CircuitSetup/Expandable-6-Channel-ESP32-Energy-Meter/Images/6-channel_v1.3_back.jpg

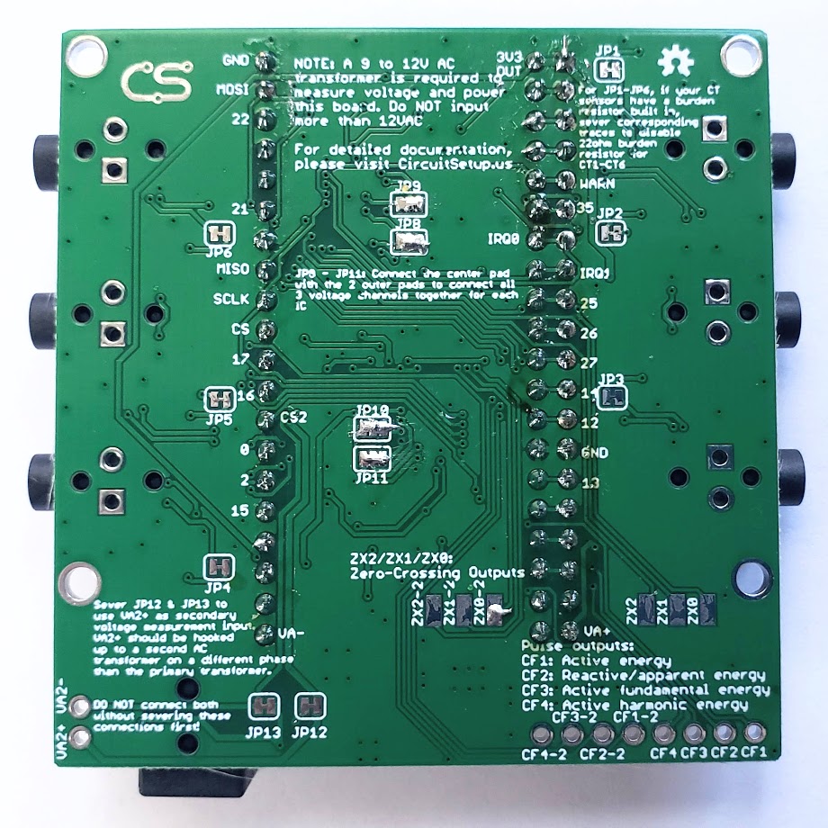
Images/6-channel_v1.3_back.jpg
