CircuitSetup/Expandable-6-Channel-ESP32-Energy-Meter/Images/20191108_202555.jpg

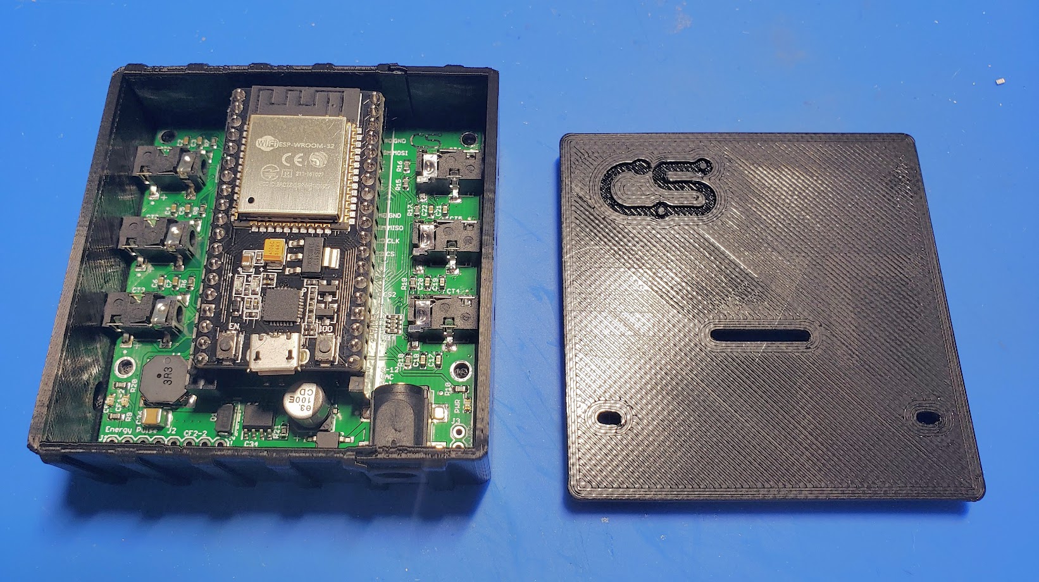
Images/20191108_202555.jpg
