CircuitSetup/Expandable-6-Channel-ESP32-Energy-Meter/Images/20191108_203225.jpg

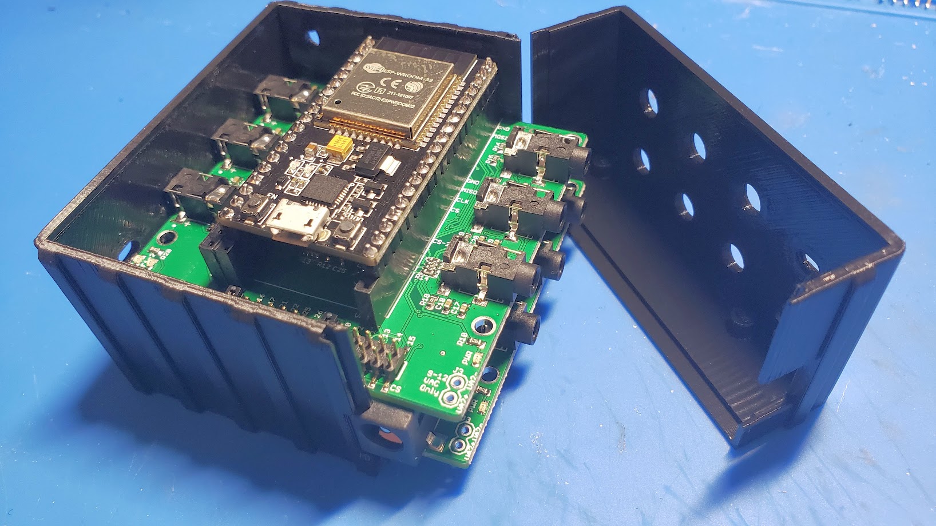
Images/20191108_203225.jpg
