CircuitSetup/Expandable-6-Channel-ESP32-Energy-Meter/Images/atm90e32-cs-6chan-full-large.jpg

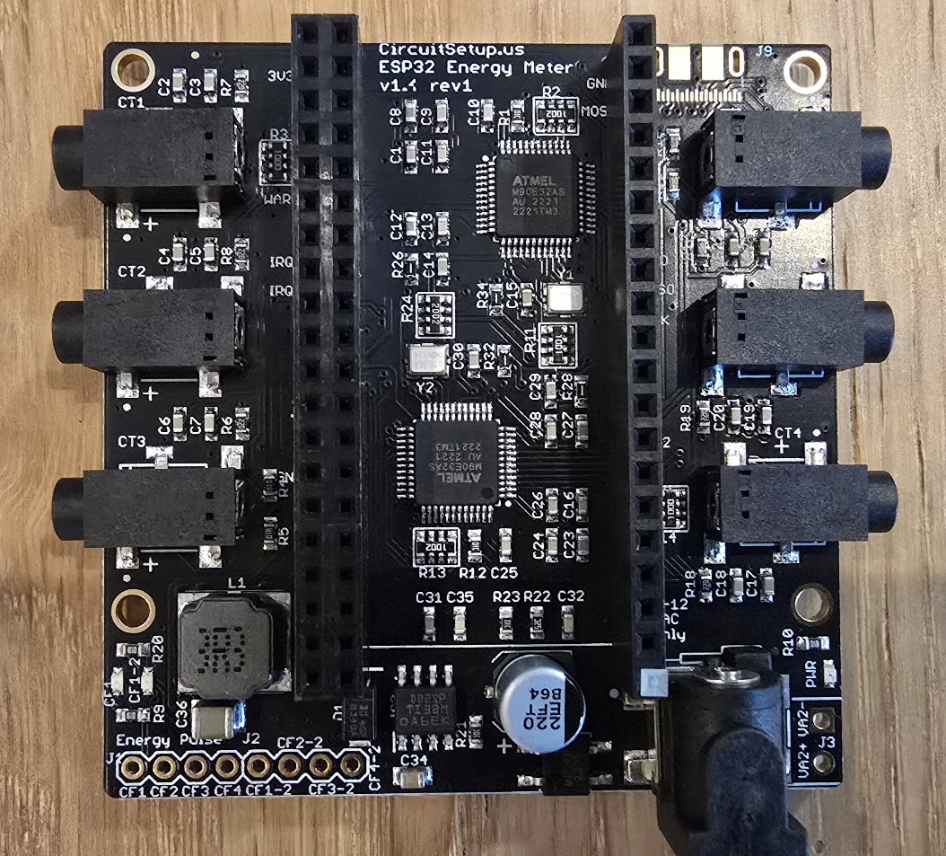
Images/atm90e32-cs-6chan-full-large.jpg
