CircuitSetup/Expandable-6-Channel-ESP32-Energy-Meter/Images/download_binary.png

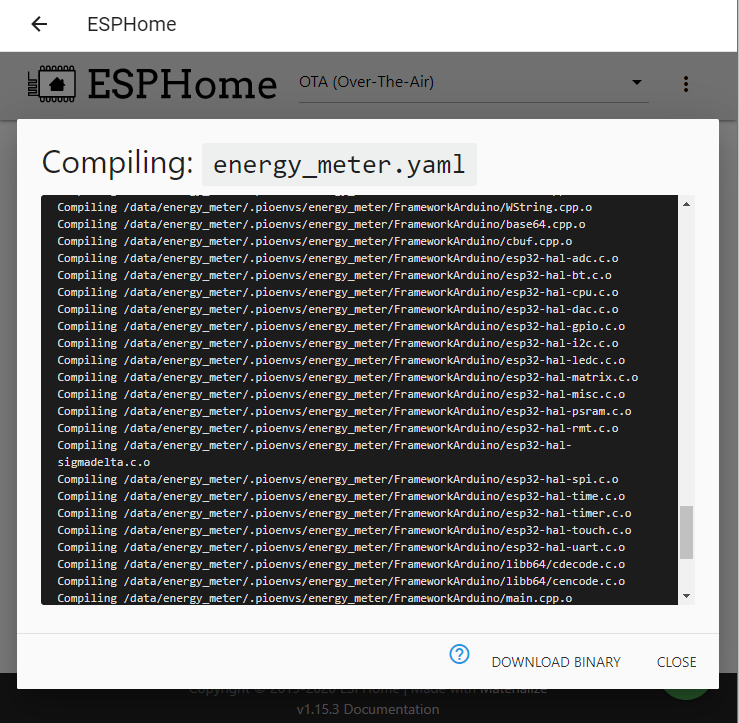
Images/download_binary.png
