CircuitSetup/Expandable-6-Channel-ESP32-Energy-Meter/Images/esphome_flasher.PNG

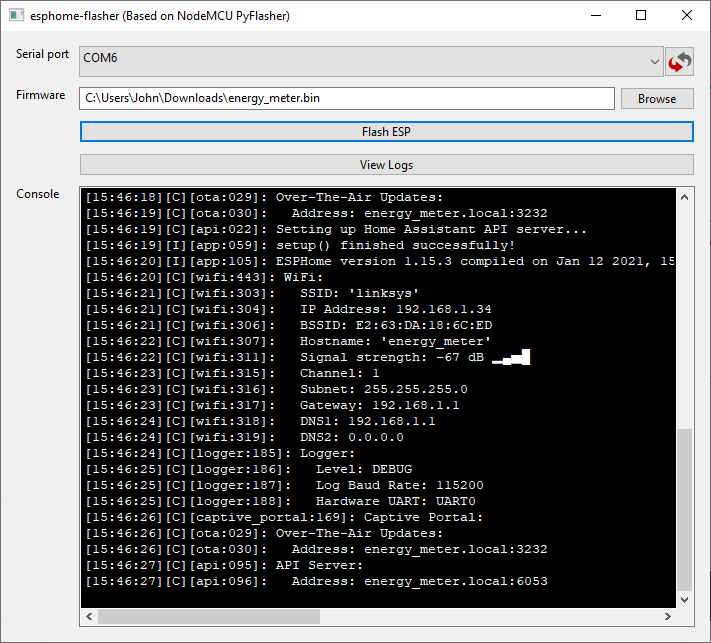
Images/esphome_flasher.PNG
