CircuitSetup/Expandable-6-Channel-ESP32-Energy-Meter/Images/esphome_main.png

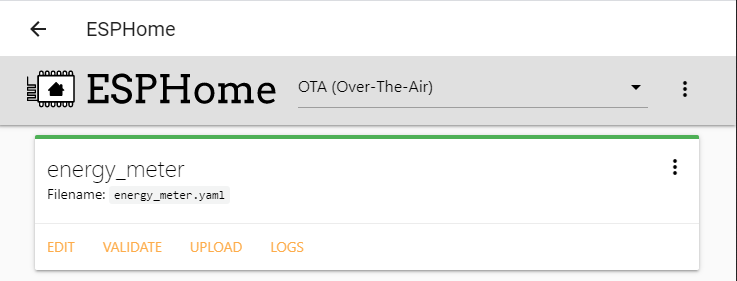
Images/esphome_main.png
