CircuitSetup/Expandable-6-Channel-ESP32-Energy-Meter/Images/home_assistant_energy2.PNG

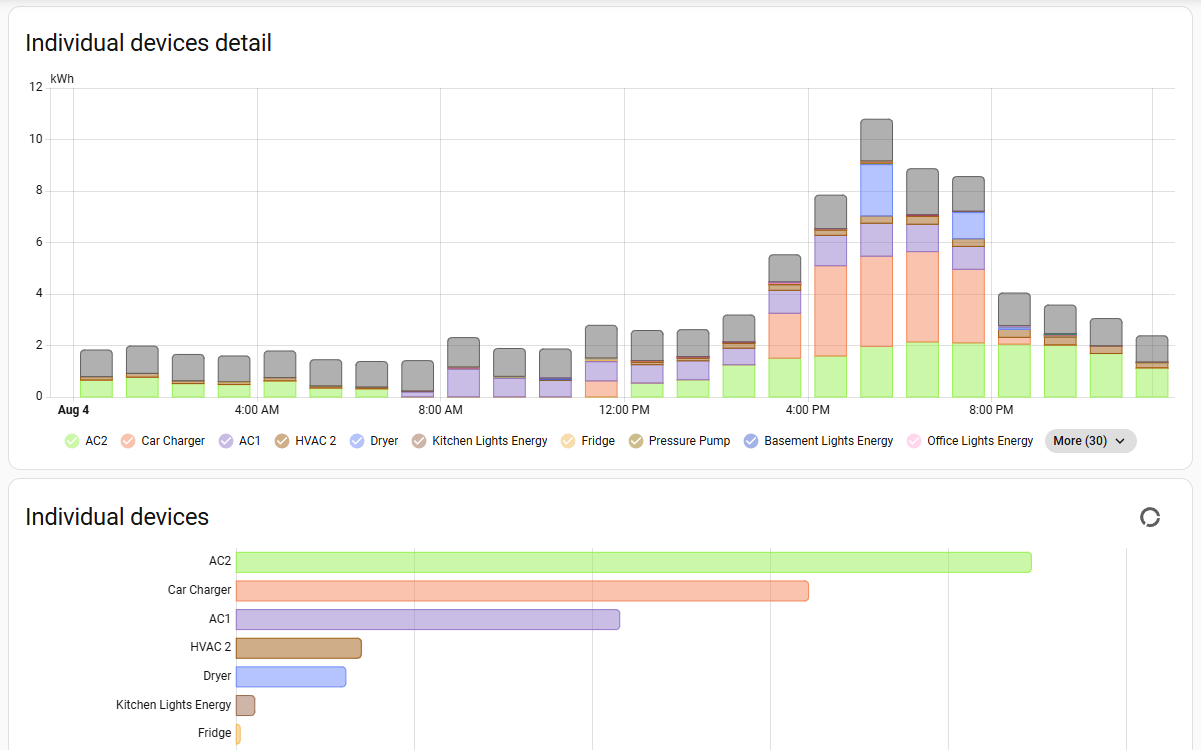
Images/home_assistant_energy2.PNG
