CircuitSetup/Expandable-6-Channel-ESP32-Energy-Meter/Software/EmonESP/docs/emoncms.png

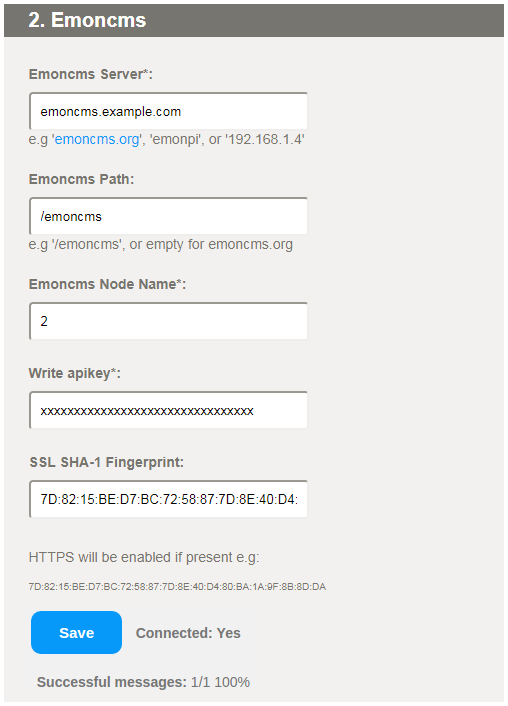
Software/EmonESP/docs/emoncms.png
