CircuitSetup/Expandable-6-Channel-ESP32-Energy-Meter/Software/EmonESP/docs/emonesp.png

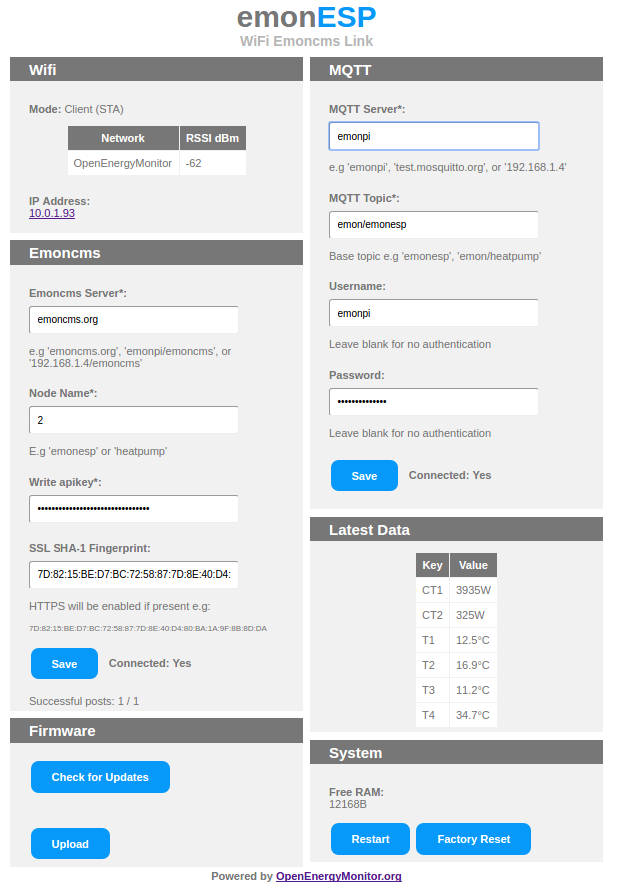
Software/EmonESP/docs/emonesp.png
