CircuitSetup/Expandable-6-Channel-ESP32-Energy-Meter/Software/EmonESP/docs/input.png

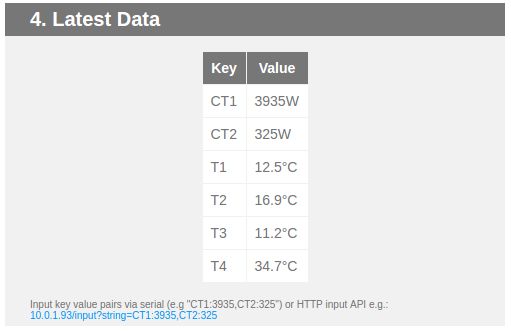
Software/EmonESP/docs/input.png
