CircuitSetup/Expandable-6-Channel-ESP32-Energy-Meter/Software/EmonESP/docs/wifi.png

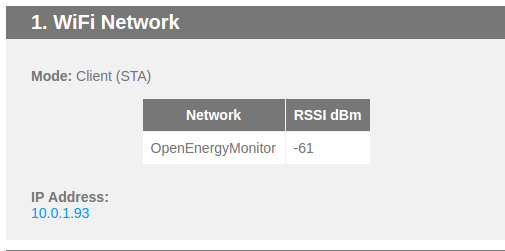
Software/EmonESP/docs/wifi.png
