CircuitSetup/Expandable-6-Channel-ESP32-Energy-Meter/Hardware/6channel_energy_meter_2piece_case_cover.stl

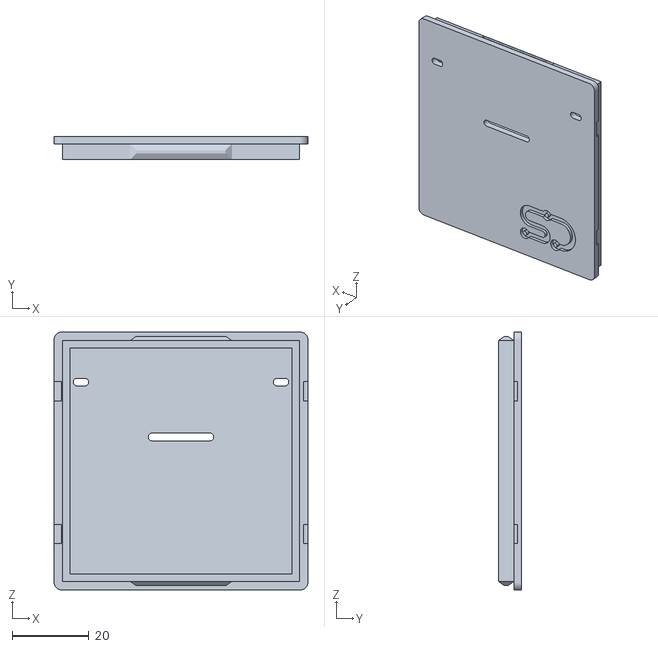
[picture p42: CAD file, 2019-11-10]
Hardware/6channel_energy_meter_2piece_case_cover.stl
66.0 x 6.00 x 67.0
