CircuitSetup/Expandable-6-Channel-ESP32-Energy-Meter/Hardware/Ethernet Adapter Cases/6channel_energy_meter_2piece_case_5-addon_ethernet_ws_large_half.stl

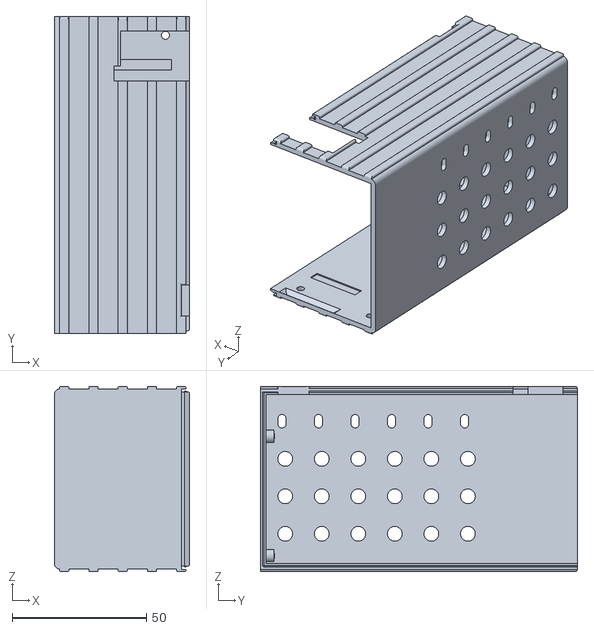
[picture p44: CAD file, 2026-02-12]
Hardware/Ethernet Adapter Cases/6channel_energy_meter_2piece_case_5-addon_ethernet_ws_large_half.stl
50.3 x 118.0 x 69.0
