CircuitSetup/Expandable-6-Channel-ESP32-Energy-Meter/Hardware/Ethernet Adapter Cases/6channel_energy_meter_2piece_case_1-addon_ethernet_ws_small_half.stl

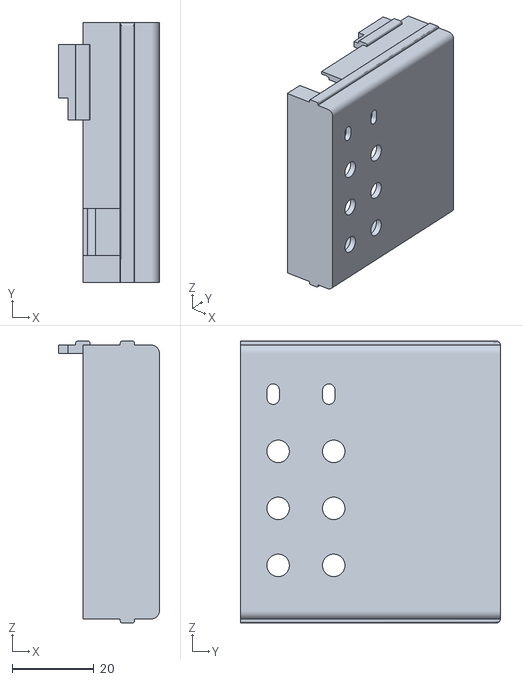
[picture p47: CAD file, 2026-02-12]
Hardware/Ethernet Adapter Cases/6channel_energy_meter_2piece_case_1-addon_ethernet_ws_small_half.stl
24.7 x 63.6 x 69.0
