CircuitSetup/Expandable-6-Channel-ESP32-Energy-Meter/Hardware/6channel_energy_meter_2piece_case_1-addon_small_half.stl

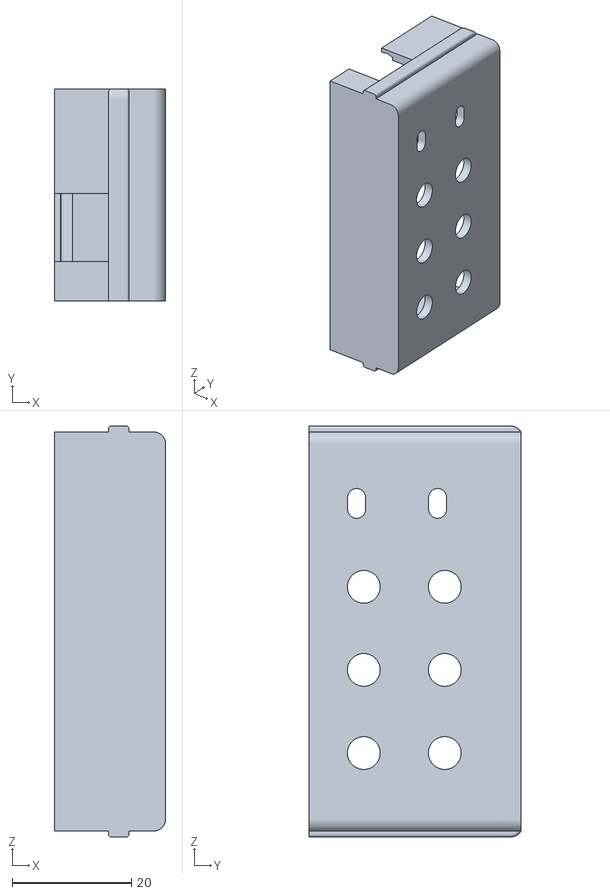
[picture p50: CAD file, 2019-11-10]
Hardware/6channel_energy_meter_2piece_case_1-addon_small_half.stl
18.6 x 35.6 x 69.0
