CircuitSetup/Expandable-6-Channel-ESP32-Energy-Meter/Hardware/Ethernet Adapter Cases/6channel_energy_meter_2piece_case_5-addon_ethernet_small_half.stl

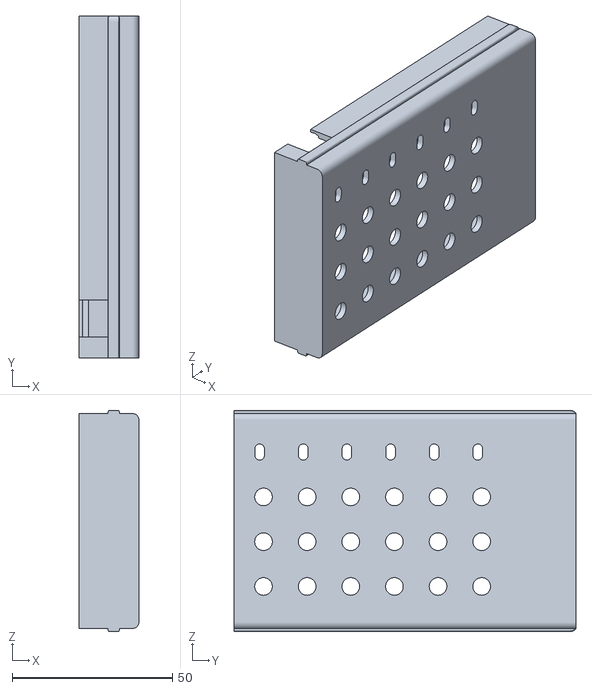
[picture p53: CAD file, 2024-08-21]
Hardware/Ethernet Adapter Cases/6channel_energy_meter_2piece_case_5-addon_ethernet_small_half.stl
18.7 x 106.6 x 69.0
