CircuitSetup/Expandable-6-Channel-ESP32-Energy-Meter/Hardware/6channel_case.stl

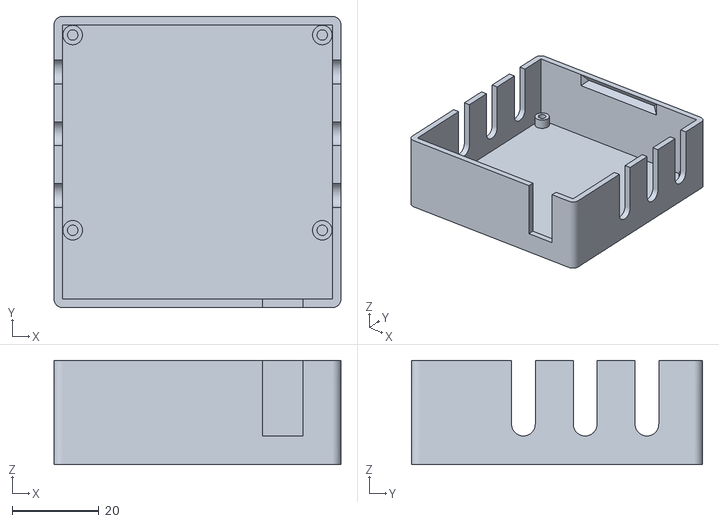
[picture p54: CAD file, 2019-10-14]
Hardware/6channel_case.stl
66.0 x 67.0 x 24.0
