CircuitSetup/Expandable-6-Channel-ESP32-Energy-Meter/Hardware/6channel_meter_case.stl

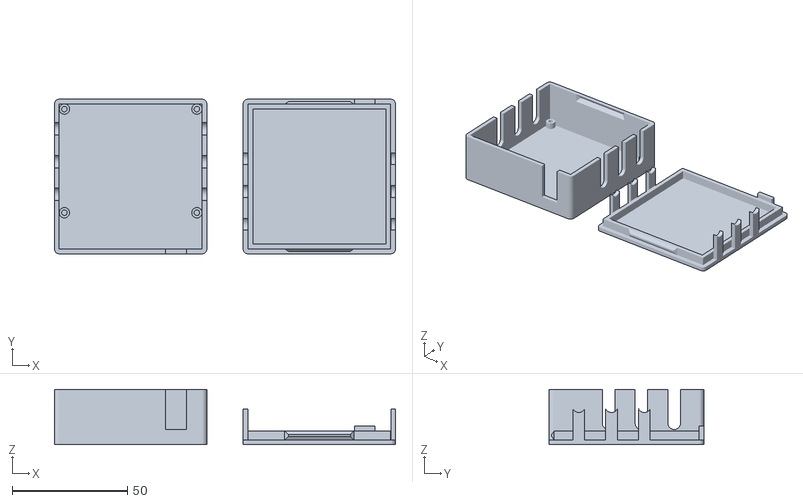
[picture p56: CAD file, 2019-10-14]
Hardware/6channel_meter_case.stl
147.7 x 67.0 x 24.0
