CircuitSetup/Expandable-6-Channel-ESP32-Energy-Meter/Hardware/Ethernet Adapter Cases/6channel_energy_meter_2piece_case_3-addon_ethernet_large_half.stl

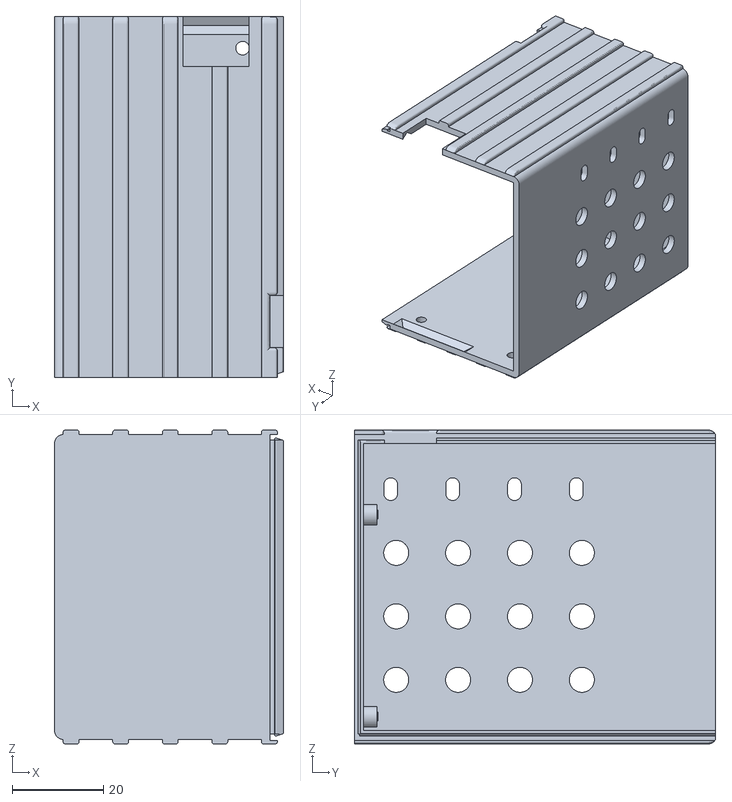
[picture p57: CAD file, 2024-08-21]
Hardware/Ethernet Adapter Cases/6channel_energy_meter_2piece_case_3-addon_ethernet_large_half.stl
50.3 x 79.4 x 69.0
