CircuitSetup/Expandable-6-Channel-ESP32-Energy-Meter/Hardware/6channel_case_lid.stl

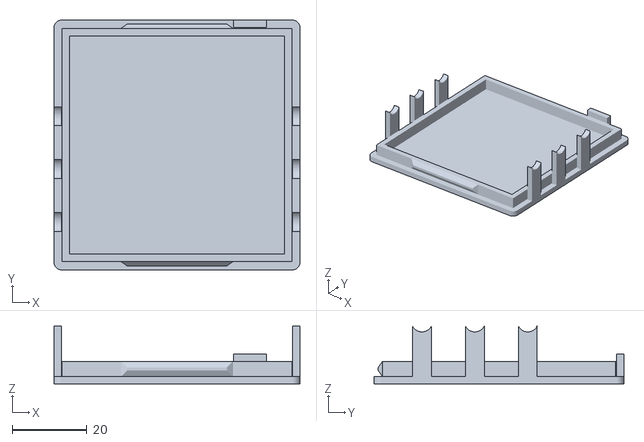
[picture p58: CAD file, 2019-10-14]
Hardware/6channel_case_lid.stl
66.0 x 67.0 x 15.5
