CircuitSetup/Expandable-6-Channel-ESP32-Energy-Meter/Images/esphome_gain_calibration.PNG

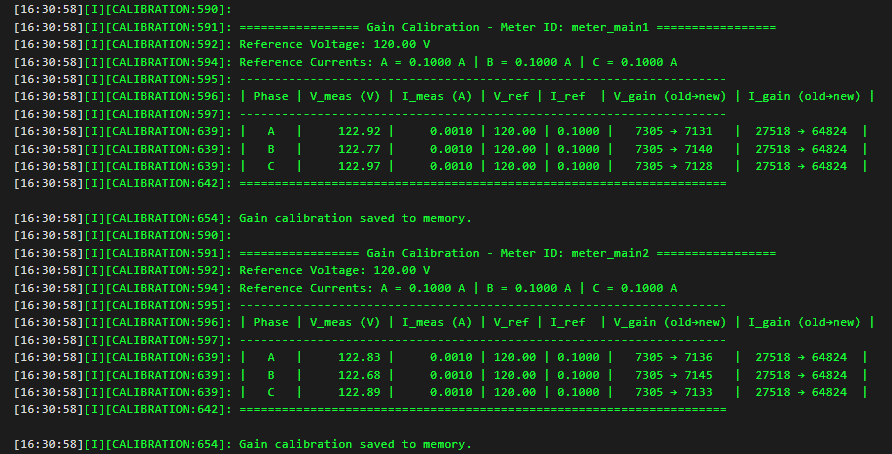
Images/esphome_gain_calibration.PNG
