CircuitSetup/Expandable-6-Channel-ESP32-Energy-Meter/Software/ESPHome/meter_sensors/6chan_addon3.yaml

# CircuitSetup 6 Channel Energy Meter 3rd Add-on board config
# Assumes jumpers are both in the 3rd position

sensor:
#IC1 AddOn 3
############
  - platform: atm90e32
    release_device: true
    #if ESP32 has an LED for GPIO2, remove jumper or ESP32 from meter stack before programming via serial
    cs_pin: 2
    id: ${addon3_id1}
    phase_a:
      voltage:
        name: "${addon3_name1} Voltage A Calibration"
        id: addon3_1_voltage_a_calibration
        accuracy_decimals: 2
        entity_category: diagnostic
        disabled_by_default: true
      current:
        name: ${ct19_name} Amps
        id: ct19Amps
      power:
        name: ${ct19_name} Watts
        id: ct19Watts
      gain_voltage: ${voltage_cal1}
      gain_ct: ${current_cal_ct19}
    phase_b:
      voltage:
        name: "${addon3_name1} Voltage B Calibration"
        id: addon3_1_voltage_b_calibration
        accuracy_decimals: 2
        entity_category: diagnostic
        disabled_by_default: true
      current:
        name: ${ct20_name} Amps
        id: ct20Amps
      power:
        name: ${ct20_name} Watts
        id: ct20Watts
      gain_voltage: ${voltage_cal1}
      gain_ct: ${current_cal_ct20}
    phase_c:
      voltage:
        name: "${addon3_name1} Voltage C Calibration"
        id: addon3_1_voltage_c_calibration
        accuracy_decimals: 2
        entity_category: diagnostic
        disabled_by_default: true
      current:
        name: ${ct21_name} Amps
        id: ct21Amps
      power:
        name: ${ct21_name} Watts
        id: ct21Watts
      gain_voltage: ${voltage_cal1}
      gain_ct: ${current_cal_ct21}
    line_frequency: ${electric_freq}
    gain_pga: 1X
    update_interval: ${update_time}
    enable_offset_calibration: ${offset_calibration}
    enable_gain_calibration: ${gain_calibration}
#IC2 AddOn 3
############
  - platform: atm90e32
    release_device: true
    cs_pin: 21
    id: ${addon3_id2}
    phase_a:
      voltage:
        name: "${addon3_name2} Voltage A Calibration"
        id: addon3_2_voltage_a_calibration
        accuracy_decimals: 2
        entity_category: diagnostic
        disabled_by_default: true
      current:
        name: ${ct22_name} Amps
        id: ct22Amps
      power:
        name: ${ct22_name} Watts
        id: ct22Watts
      gain_voltage: ${voltage_cal2}
      gain_ct: ${current_cal_ct22}
    phase_b:
      voltage:
        name: "${addon3_name2} Voltage B Calibration"
        id: addon3_2_voltage_b_calibration
        accuracy_decimals: 2
        entity_category: diagnostic
        disabled_by_default: true
      current:
        name: ${ct23_name} Amps
        id: ct23Amps
      power:
        name: ${ct23_name} Watts
        id: ct23Watts
      gain_voltage: ${voltage_cal2}
      gain_ct: ${current_cal_ct23}
    phase_c:
      voltage:
        name: "${addon3_name2} Voltage C Calibration"
        id: addon3_2_voltage_c_calibration
        accuracy_decimals: 2
        entity_category: diagnostic
        disabled_by_default: true
      current:
        name: ${ct24_name} Amps
        id: ct24Amps
      power:
        name: ${ct24_name} Watts
        id: ct24Watts
      gain_voltage: ${voltage_cal2}
      gain_ct: ${current_cal_ct24}
    line_frequency: ${electric_freq}
    gain_pga: 1X
    update_interval: ${update_time}
    enable_offset_calibration: ${offset_calibration}
    enable_gain_calibration: ${gain_calibration}

#Total Amps AddOn3
  - platform: template
    name: ${friendly_name} Total Amps Add-on3
    id: totalAmpsAddOn3
    lambda: return id(ct19Amps).state + id(ct20Amps).state + id(ct21Amps).state + id(ct22Amps).state + id(ct23Amps).state + id(ct24Amps).state ;
    accuracy_decimals: 2
    unit_of_measurement: A
    device_class: current
    update_interval: ${update_time}

#Total Watts AddOn3
  - platform: template
    name: ${friendly_name} Total Watts Add-on3
    id: totalWattsAddOn3
    lambda: return id(ct19Watts).state + id(ct20Watts).state + id(ct21Watts).state + id(ct22Watts).state + id(ct23Watts).state + id(ct24Watts).state ;
    accuracy_decimals: 2
    unit_of_measurement: W
    device_class: power
    update_interval: ${update_time}
