CircuitSetup/Expandable-6-Channel-ESP32-Energy-Meter/Software/ESPHome/calibration/6chan_addon1_calibration.yaml

# Details: https://esphome.io/components/sensor/atm90e32.html#calibration
# Semi-automatic Calibration Buttons
####################################
button:
  - platform: atm90e32
    id: ${addon1_id1}
    run_offset_calibration:
      name: "1. Run ${addon1_name1} Offset Cal"
      disabled_by_default: true
    clear_offset_calibration:
      name: "z1. Clear ${addon1_name1} Offset Cal"
      disabled_by_default: true
    run_power_offset_calibration:
      name: "2. Run ${addon1_name1} Power Offset Cal"
      disabled_by_default: true
    clear_power_offset_calibration:
      name: "z2. Clear ${addon1_name1} Power Offset Cal"
      disabled_by_default: true
    run_gain_calibration:
      name: "3. Run ${addon1_name1} Gain Cal"
      disabled_by_default: true
    clear_gain_calibration:
      name: "z3. Clear ${addon1_name1} Gain Cal"
      disabled_by_default: true

  - platform: atm90e32
    id: ${addon1_id2}
    run_offset_calibration:
      name: "1. Run ${addon1_name2} Offset Cal"
      disabled_by_default: true
    clear_offset_calibration:
      name: "z1. Clear ${addon1_name2} Offset Cal"
      disabled_by_default: true
    run_power_offset_calibration:
      name: "2. Run ${addon1_name2} Power Offset Cal"
      disabled_by_default: true
    clear_power_offset_calibration:
      name: "z2. Clear ${addon1_name2} Power Offset Cal"
      disabled_by_default: true
    run_gain_calibration:
      name: "3. Run ${addon1_name2} Gain Cal"
      disabled_by_default: true
    clear_gain_calibration:
      name: "z3. Clear ${addon1_name2} Gain Cal"
      disabled_by_default: true

# V & I Calibration Reference Fields
####################################
# Use these to input a known value being measured by a CT or voltage transformer
number:
  - platform: atm90e32
    id: ${addon1_id1}
    reference_voltage:
      # will copy to phase_b/c for calibration reference
      phase_a:
        name: "${addon1_name1} Ref V 1"
        min_value: 0.0
        max_value: 260.0
        step: 0.1
        disabled_by_default: true
    reference_current:
      phase_a:
        name: "${ct7_name} Ref Current"
        min_value: 0.0
        max_value: 200.0
        step: 0.1
        disabled_by_default: true
      phase_b:
        name: "${ct8_name} Ref Current"
        min_value: 0.0
        max_value: 200.0
        step: 0.1
        disabled_by_default: true
      phase_c:
        name: "${ct9_name} Ref Current"
        min_value: 0.0
        max_value: 200.0
        step: 0.1
        disabled_by_default: true

  - platform: atm90e32
    id: ${addon1_id2}
    reference_voltage:
      # needed to calibrate voltage registers even if not output
      phase_a:
        name: "${addon1_name2} Ref V 2" 
        min_value: 0.0
        max_value: 260.0
        step: 0.1
        disabled_by_default: true
    reference_current:
      phase_a:
        name: "${ct10_name} Ref Current"
        min_value: 0.0
        max_value: 200.0
        step: 0.1
        disabled_by_default: true
      phase_b:
        name: "${ct11_name} Ref Current"
        min_value: 0.0
        max_value: 200.0
        step: 0.1
        disabled_by_default: true
      phase_c:
        name: "${ct12_name} Ref Current"
        min_value: 0.0
        max_value: 200.0
        step: 0.1
        disabled_by_default: true
