CircuitSetup/Expandable-6-Channel-ESP32-Energy-Meter/Software/ESPHome/calibration/6chan_addon2_calibration.yaml

# Details: https://esphome.io/components/sensor/atm90e32.html#calibration
# Semi-automatic Calibration Buttons
####################################
button:
  - platform: atm90e32
    id: ${addon2_id1}
    run_offset_calibration:
      name: "1. Run ${addon2_name1} Offset Cal"
      disabled_by_default: true
    clear_offset_calibration:
      name: "z1. Clear ${addon2_name1} Offset Cal"
      disabled_by_default: true
    run_power_offset_calibration:
      name: "2. Run ${addon2_name1} Power Offset Cal"
      disabled_by_default: true
    clear_power_offset_calibration:
      name: "z2. Clear ${addon2_name1} Power Offset Cal"
      disabled_by_default: true
    run_gain_calibration:
      name: "3. Run ${addon2_name1} Gain Cal"
      disabled_by_default: true
    clear_gain_calibration:
      name: "z3. Clear ${addon2_name1} Gain Cal"
      disabled_by_default: true

  - platform: atm90e32
    id: ${addon2_id2}
    run_offset_calibration:
      name: "1. Run ${addon2_name2} Offset Cal"
      disabled_by_default: true
    clear_offset_calibration:
      name: "z1. Clear ${addon2_name2} Offset Cal"
      disabled_by_default: true
    run_power_offset_calibration:
      name: "2. Run ${addon2_name2} Power Offset Cal"
      disabled_by_default: true
    clear_power_offset_calibration:
      name: "z2. Clear ${addon2_name2} Power Offset Cal"
      disabled_by_default: true
    run_gain_calibration:
      name: "3. Run ${addon2_name2} Gain Cal"
      disabled_by_default: true
    clear_gain_calibration:
      name: "z3. Clear ${addon2_name2} Gain Cal"
      disabled_by_default: true

# V & I Calibration Reference Fields
####################################
# Use these to input a known value being measured by a CT or voltage transformer
number:
  - platform: atm90e32
    id: ${addon2_id1}
    reference_voltage:
      # will copy to phase_b/c for calibration reference
      phase_a:
        name: "${addon2_name1} Ref V 1"
        min_value: 0.0
        max_value: 260.0
        step: 0.1
        disabled_by_default: true
    reference_current:
      phase_a:
        name: "${ct13_name} Ref Current"
        min_value: 0.0
        max_value: 200.0
        step: 0.1
        disabled_by_default: true
      phase_b:
        name: "${ct14_name} Ref Current"
        min_value: 0.0
        max_value: 200.0
        step: 0.1
        disabled_by_default: true
      phase_c:
        name: "${ct15_name} Ref Current"
        min_value: 0.0
        max_value: 200.0
        step: 0.1
        disabled_by_default: true

  - platform: atm90e32
    id: ${addon2_id2}
    reference_voltage:
      # needed to calibrate voltage registers even if not output
      phase_a:
        name: "${addon2_name2} Ref V 2" 
        min_value: 0.0
        max_value: 260.0
        step: 0.1
        disabled_by_default: true
    reference_current:
      phase_a:
        name: "${ct16_name} Ref Current"
        min_value: 0.0
        max_value: 200.0
        step: 0.1
        disabled_by_default: true
      phase_b:
        name: "${ct17_name} Ref Current"
        min_value: 0.0
        max_value: 200.0
        step: 0.1
        disabled_by_default: true
      phase_c:
        name: "${ct18_name} Ref Current"
        min_value: 0.0
        max_value: 200.0
        step: 0.1
        disabled_by_default: true
